hbh7/DoorSystem/models/Cup.stl

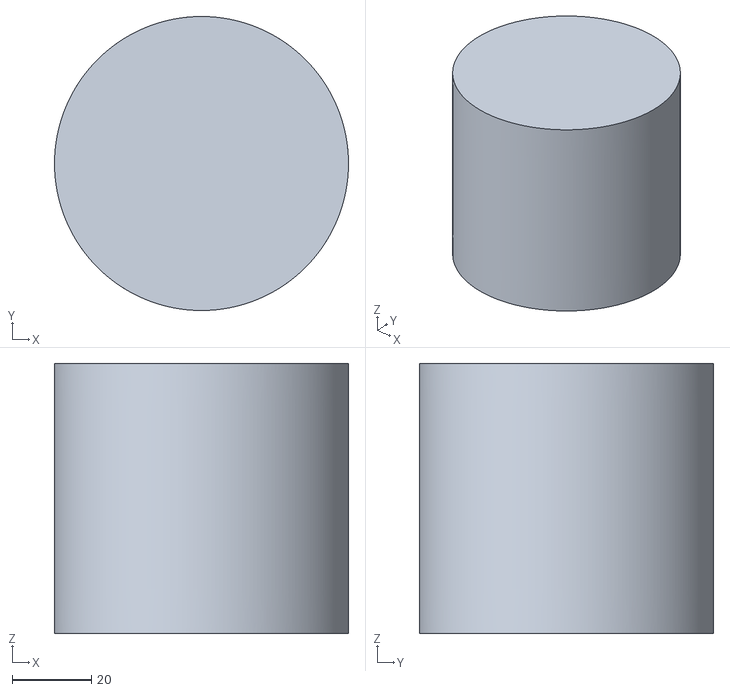
[picture p18: CAD file, 2023-09-29]
models/Cup.stl
74.0 x 74.0 x 68.0
