hbh7/DoorSystem/models/Servo Wheel 1.STL

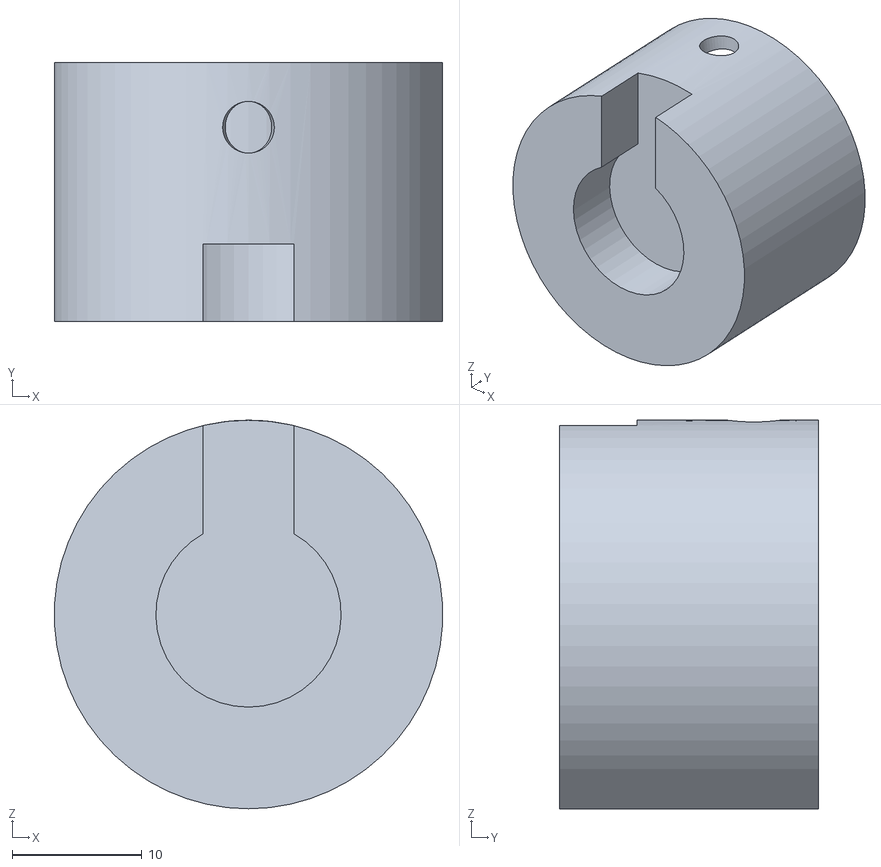
[picture p19: CAD file, 2023-09-29]
models/Servo Wheel 1.STL
30.0 x 20.0 x 30.0
