hbh7/DoorSystem/models/Part4.SLDPRT

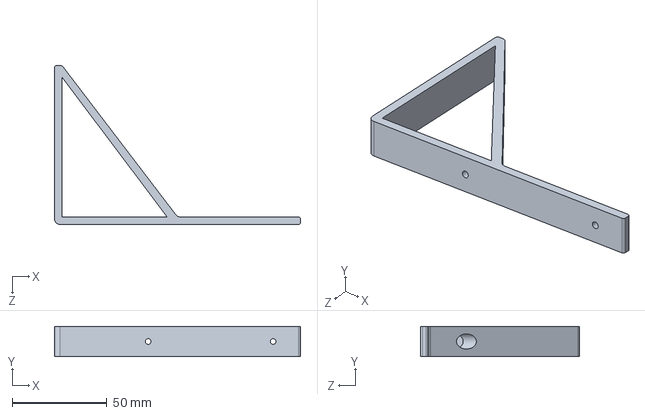
[picture p20: CAD file, 2023-09-29]
models/Part4.SLDPRT
130.0 x 16.0 x 84.0 mm
